Caveatron/Caveatron_SV/RevA/mechanical/STEP files/LCD Clamp v2.step

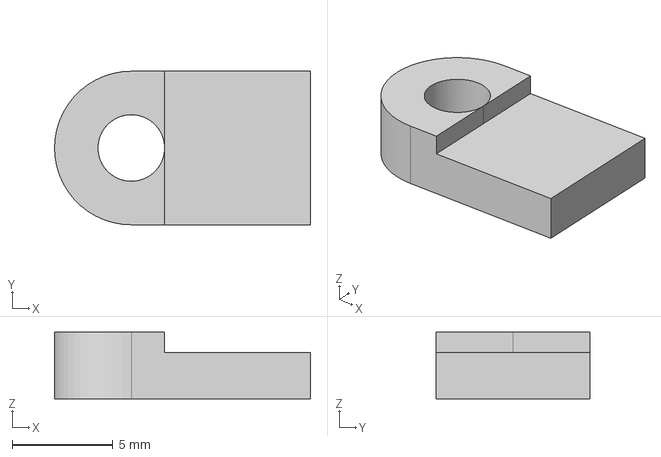
[picture p69: CAD file, 2021-04-27, an earlier design]
RevA/mechanical/STEP files/LCD Clamp v2.step
12.7 x 7.62 x 3.30 mm
