Caveatron/Caveatron_SV/RevA/mechanical/STEP files/Buzzer Clamp v2.step

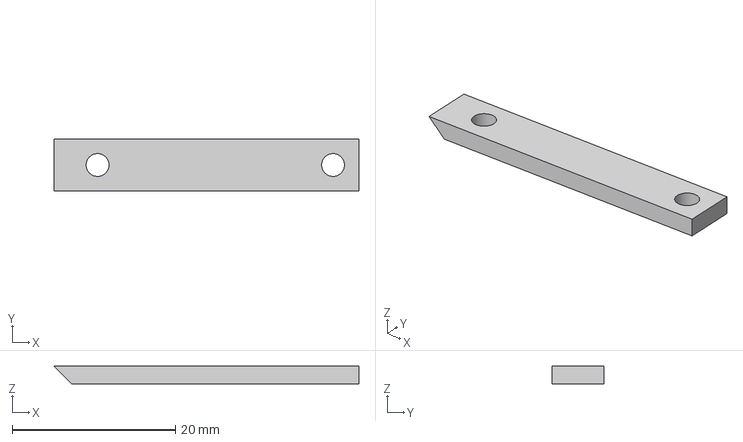
[picture p70: CAD file, 2021-04-27, an earlier design]
RevA/mechanical/STEP files/Buzzer Clamp v2.step
37.3 x 6.35 x 2.16 mm
