Caveatron/Caveatron_SV/RevA/mechanical/STEP files/LRF Bracket Top v2.step

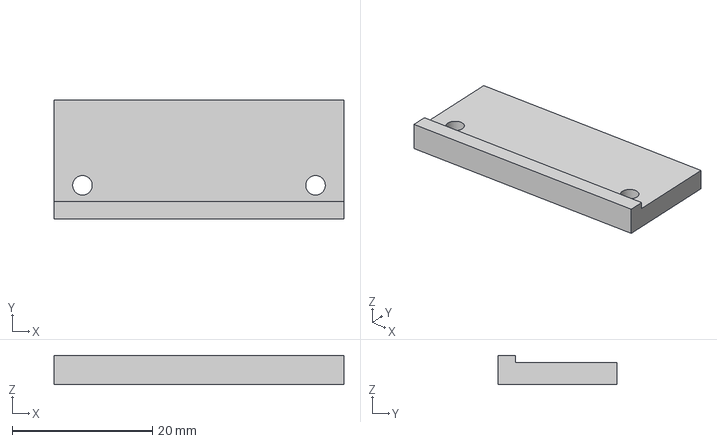
[picture p71: CAD file, 2021-04-27, an earlier design]
RevA/mechanical/STEP files/LRF Bracket Top v2.step
41.4 x 17.0 x 4.19 mm
