Caveatron/Caveatron_SV/RevA/mechanical/STEP files/Battery Clamp v1.step

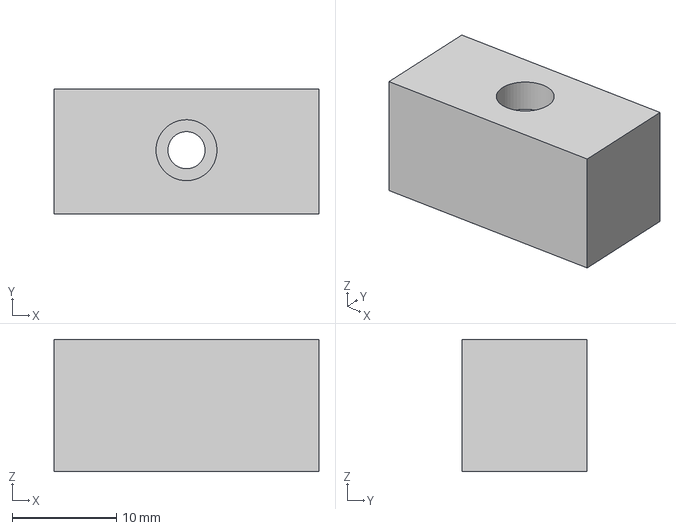
[picture p72: CAD file, 2021-04-27, an earlier design]
RevA/mechanical/STEP files/Battery Clamp v1.step
25.4 x 11.9 x 12.7 mm
